kramerbastian/doppeltraktion/assets/readme/bottom_base_right.png

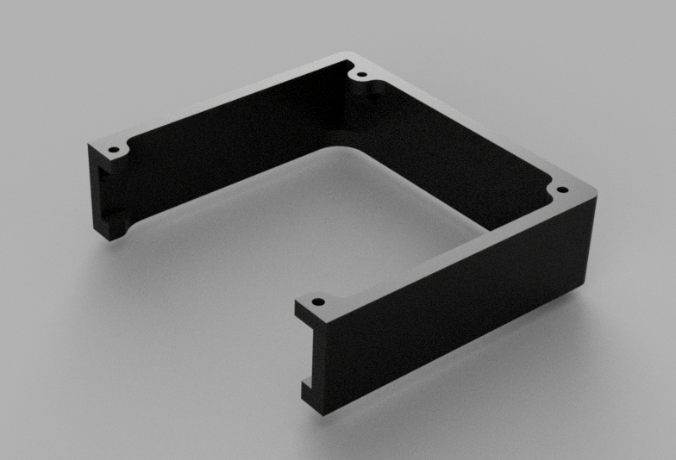
assets/readme/bottom_base_right.png
