kramerbastian/doppeltraktion/assets/readme/display_cover.png

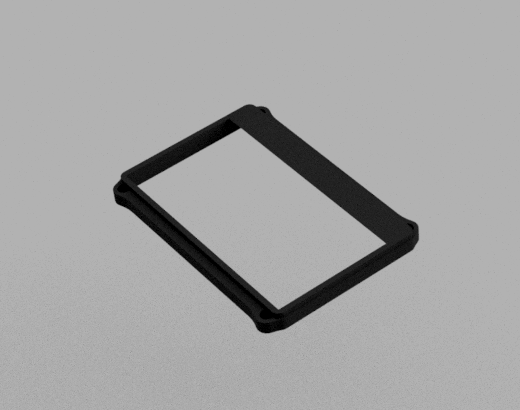
assets/readme/display_cover.png
